printicus/For-Voron-Printers/MiniBurner_XL_Toolhead/Images/Pusher_example_location.jpg

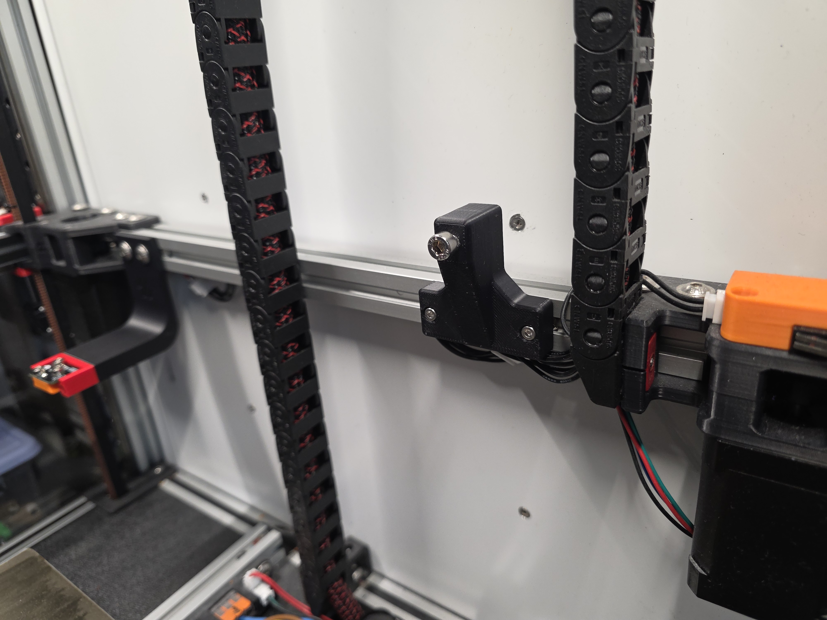
MiniBurner_XL_Toolhead/Images/Pusher_example_location.jpg
