printicus/For-Voron-Printers/MiniBurner_XL_Toolhead/Images/StealthChanger_Shuttle_04.jpg

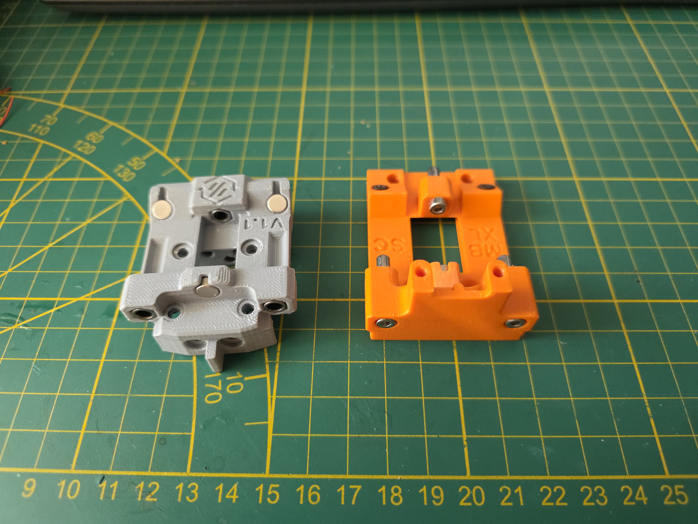
MiniBurner_XL_Toolhead/Images/StealthChanger_Shuttle_04.jpg
