printicus/For-Voron-Printers/MiniBurner_XL_Toolhead/Images/Toolhead_03.jpg

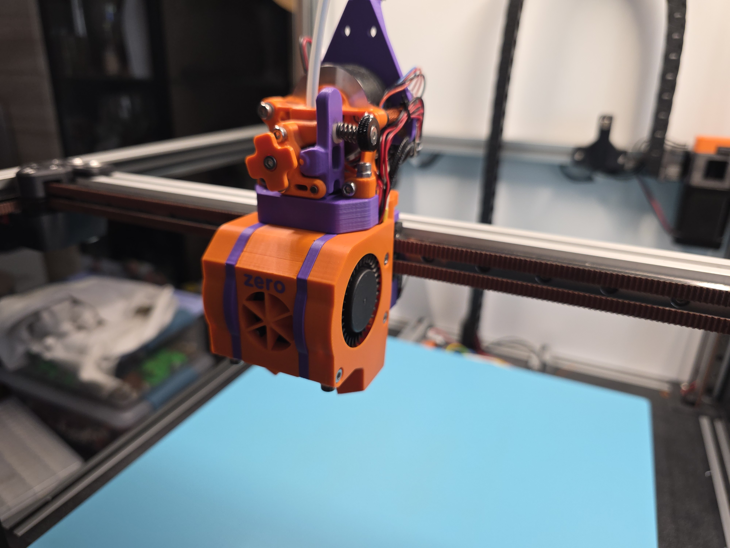
MiniBurner_XL_Toolhead/Images/Toolhead_03.jpg
