printicus/For-Voron-Printers/MiniBurner_XL_Toolhead/Images/Toolhead_05.jpg

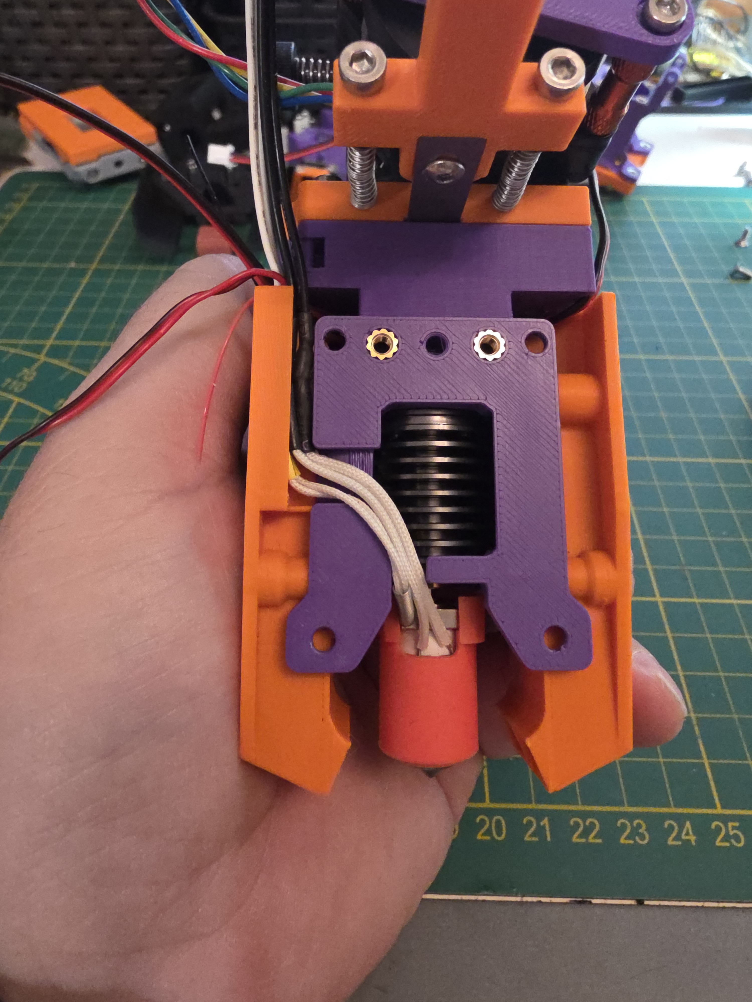
MiniBurner_XL_Toolhead/Images/Toolhead_05.jpg
