printicus/For-Voron-Printers/MiniBurner_XL_Toolhead/Images/Toolhead_06.jpg

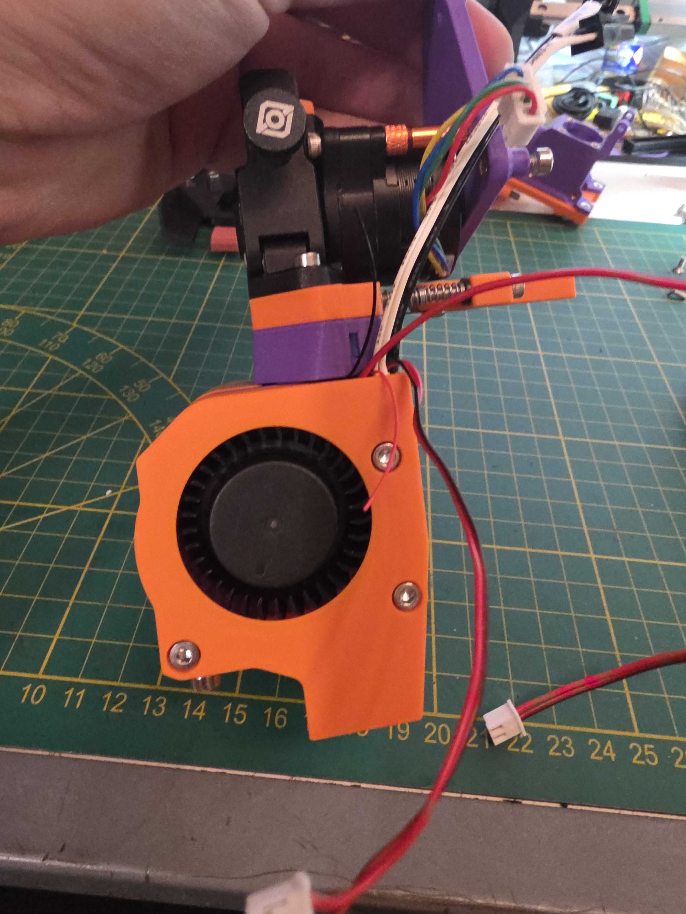
MiniBurner_XL_Toolhead/Images/Toolhead_06.jpg
