printicus/For-Voron-Printers/MiniBurner_XL_Toolhead/Images/Toolhead_08.jpg

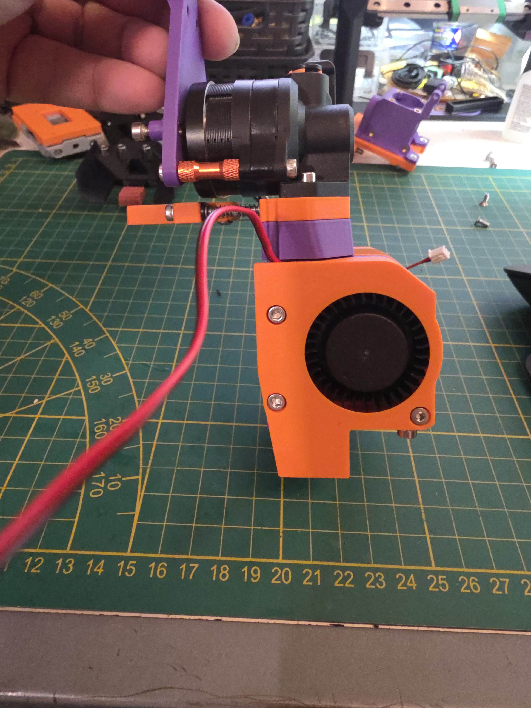
MiniBurner_XL_Toolhead/Images/Toolhead_08.jpg
