printicus/For-Voron-Printers/MiniBurner_XL_Toolhead/Images/Toolhead_09.jpg

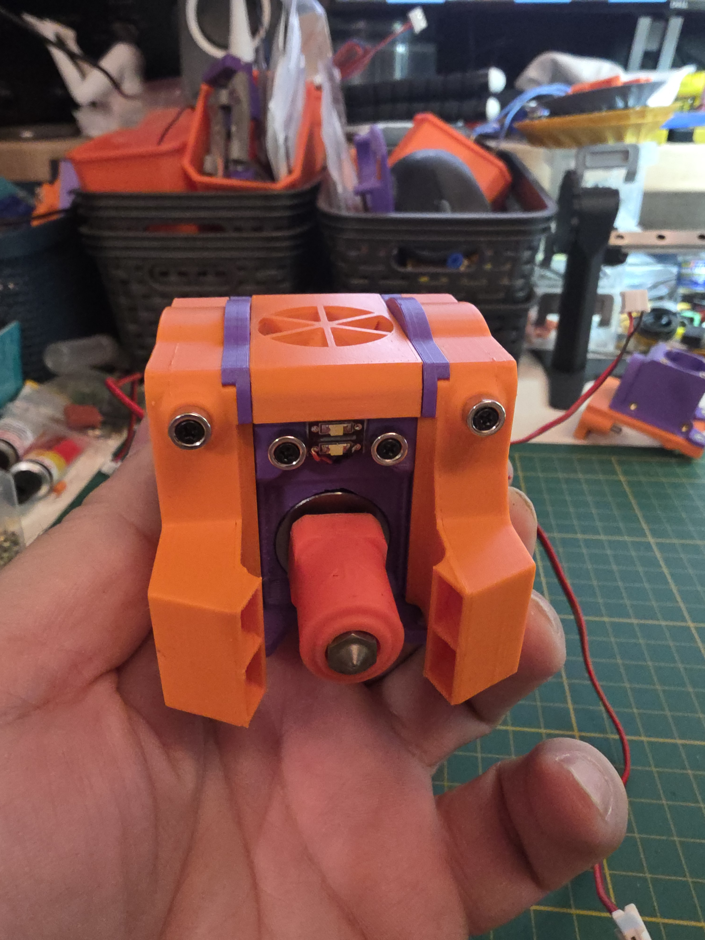
MiniBurner_XL_Toolhead/Images/Toolhead_09.jpg
