printicus/For-Voron-Printers/MiniBurner_XL_Toolhead/Images/Umbilical_01.jpg

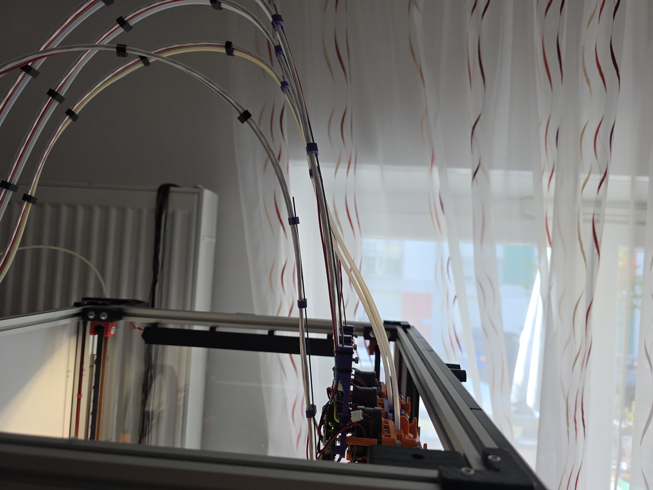
MiniBurner_XL_Toolhead/Images/Umbilical_01.jpg
