printicus/For-Voron-Printers/Voron 2.4 Left Front Skirt With Power Switch/Images/Image02.jpg

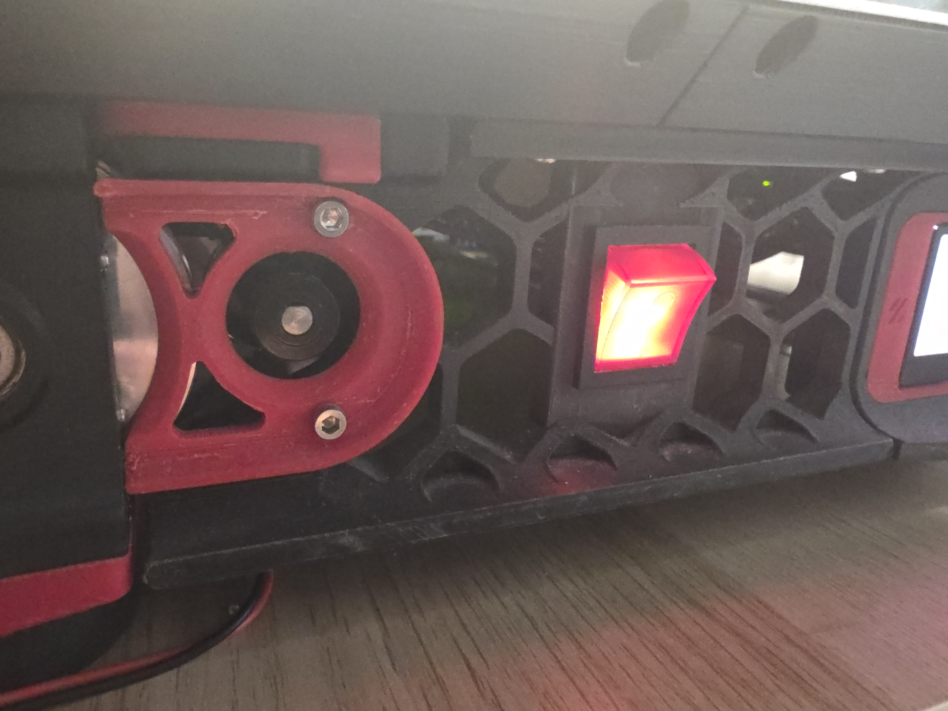
Voron 2.4 Left Front Skirt With Power Switch/Images/Image02.jpg
