printicus/For-Voron-Printers/Belt-Clamp-for-Voron-2.4-and-Trident/CAD/Left Side.step

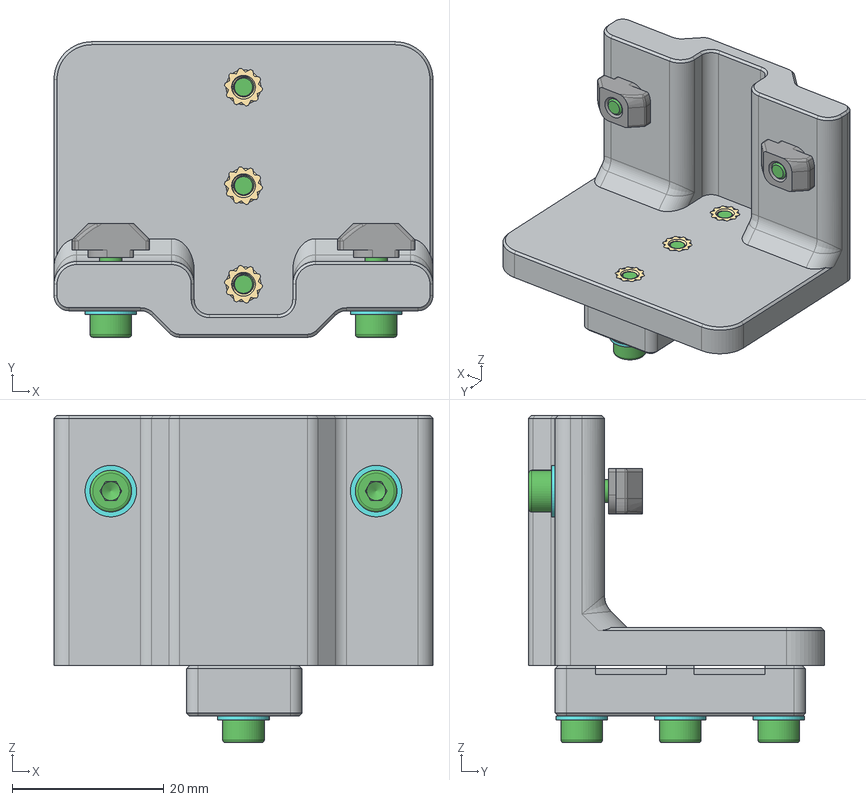
[picture p46: CAD file, 2025-07-18]
Belt-Clamp-for-Voron-2.4-and-Trident/CAD/Left Side.step
50.0 x 39.0 x 43.2 mm
XY belt clamp - left
Heat Insert M3 Short 5x4 x 3
XY belt clamp - common
M3 Washer x 5
M3x12 hex socket cap screw x 5
M3 Hammerhead T-Nut x 2
