printicus/For-Voron-Printers/Belt-Clamp-for-Voron-2.4-and-Trident/STL/XY belt clamp - right - part a.stl

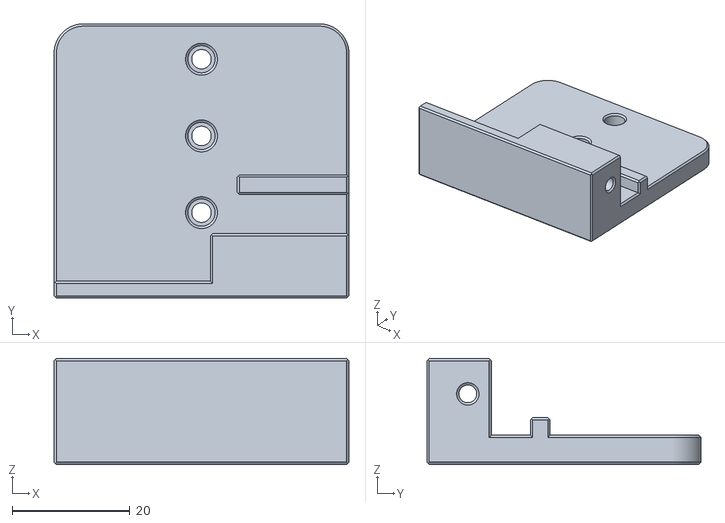
[picture p47: CAD file, 2025-07-19]
Belt-Clamp-for-Voron-2.4-and-Trident/STL/XY belt clamp - right - part a.stl
50.0 x 46.5 x 18.0
