printicus/For-Voron-Printers/MiniBurner_XL_Toolhead/STL/Extruders/For_Orbiter_v2/Orbiter_v2_CAN_PCB_Umbilical_Mount_for_max_2mm_wire.stl

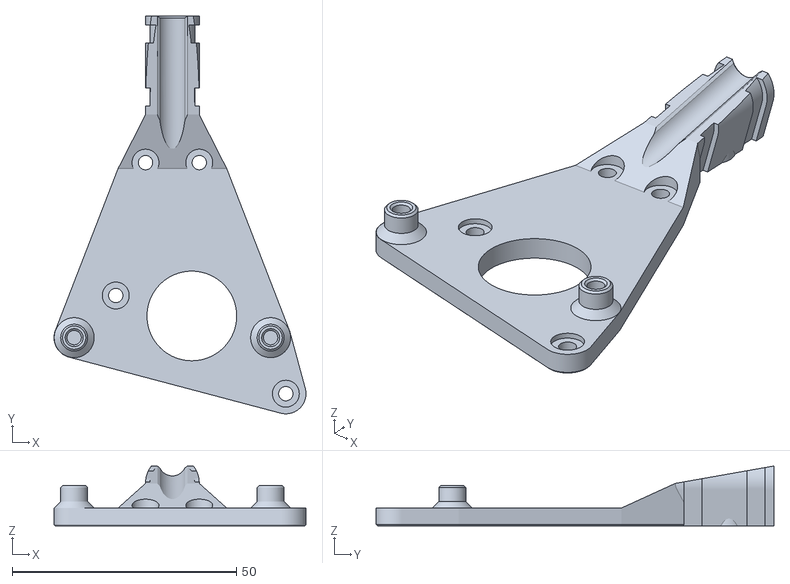
[picture p48: CAD file, 2025-08-24]
MiniBurner_XL_Toolhead/STL/Extruders/For_Orbiter_v2/Orbiter_v2_CAN_PCB_Umbilical_Mount_for_max_2mm_wire.stl
56.2 x 88.7 x 13.4
