printicus/For-Voron-Printers/MiniBurner_XL_Toolhead/STL/Extruders/For_Sherpa-Mini/Sherpa_Mini_CAN_PCB_Umbilical_Mount_for_max_2mm_wire.stl

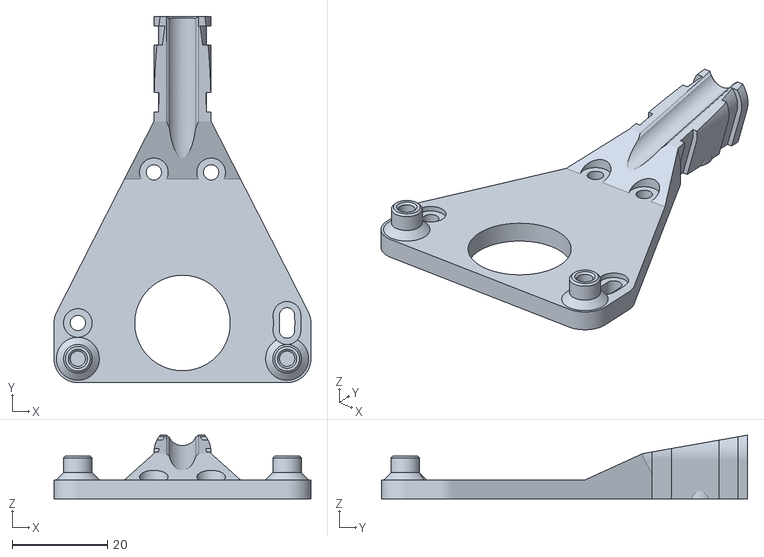
[picture p49: CAD file, 2025-08-24]
MiniBurner_XL_Toolhead/STL/Extruders/For_Sherpa-Mini/Sherpa_Mini_CAN_PCB_Umbilical_Mount_for_max_2mm_wire.stl
53.8 x 76.7 x 13.4
