printicus/For-Voron-Printers/MiniBurner_XL_Toolhead/STL/For_Volcano_Lenght_Nozzle/Right_Fan_Support_-_Sunon.stl

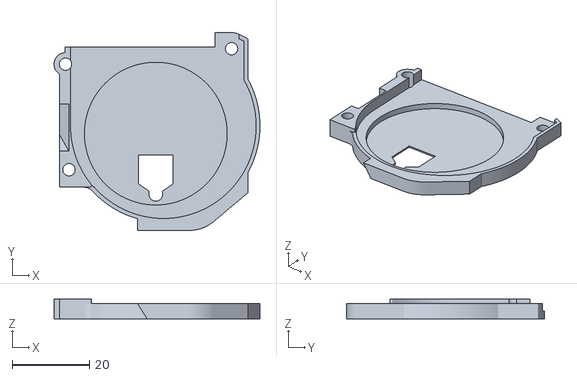
[picture p50: CAD file, 2025-08-24]
MiniBurner_XL_Toolhead/STL/For_Volcano_Lenght_Nozzle/Right_Fan_Support_-_Sunon.stl
53.4 x 51.3 x 5.10
