printicus/For-Voron-Printers/OV9726 Nozzle Camera/STL/Bottom.stl

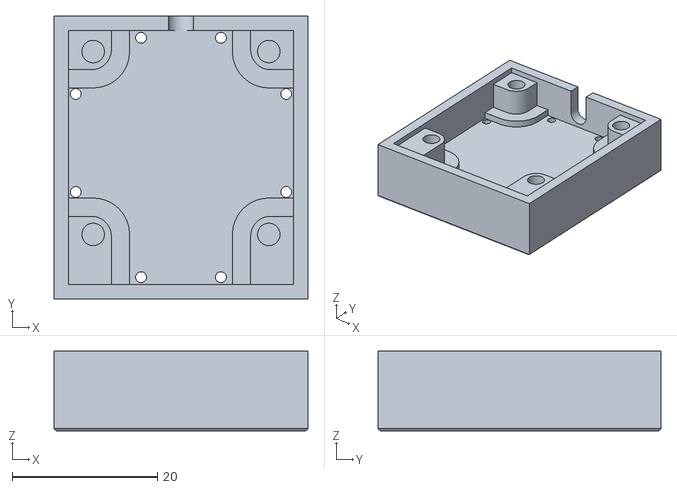
[picture p51: CAD file, 2025-07-21]
OV9726 Nozzle Camera/STL/Bottom.stl
35.0 x 39.0 x 11.0
