printicus/For-Voron-Printers/Voron 2.4 Left Front Skirt With Power Switch/CAD/front_skirt_a_300_with_power_switch-Body.step

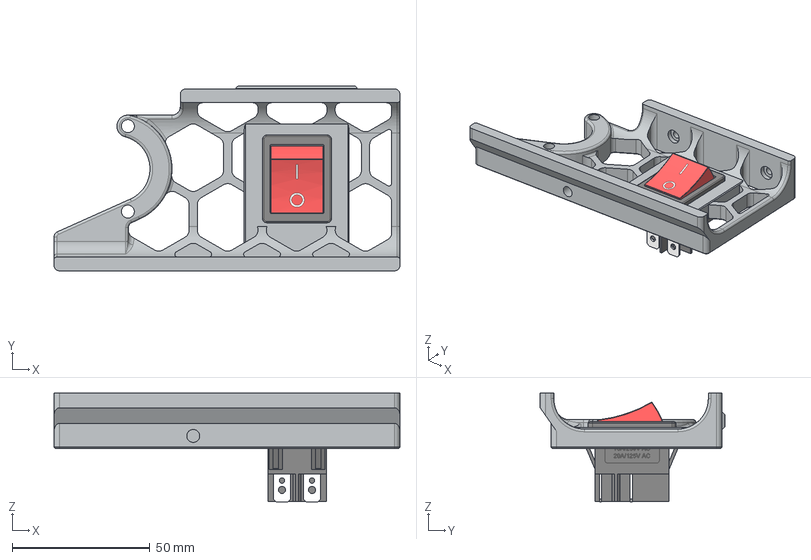
[picture p52: CAD file, 2025-07-19]
Voron 2.4 Left Front Skirt With Power Switch/CAD/front_skirt_a_300_with_power_switch-Body.step
125.5 x 67.0 x 39.4 mm
front_skirt_a_300_with_power_switch-Body
Case
Button
