printicus/For-Voron-Printers/Belt-Clamp-for-Voron-2.4-and-Trident/STL/XY belt clamp - left.stl

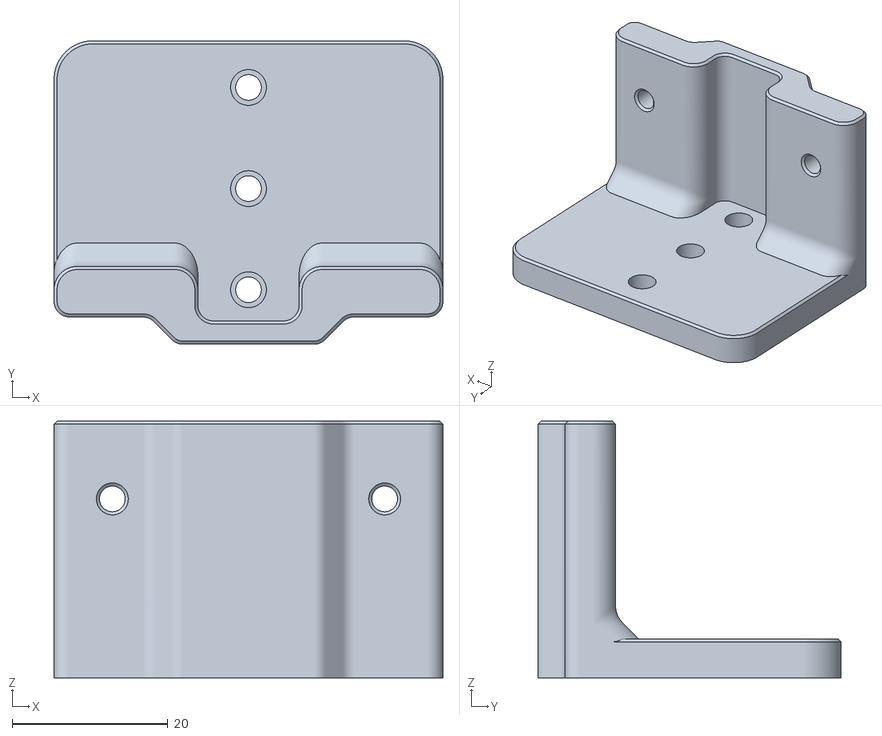
[picture p53: CAD file, 2025-07-18]
Belt-Clamp-for-Voron-2.4-and-Trident/STL/XY belt clamp - left.stl
50.0 x 39.0 x 33.0
