printicus/For-Voron-Printers/MiniBurner_XL_Toolhead/CAD/Extruders/Sherpa_Mini_CAN_PCB_Umbilical_Mount_for_3x0.3_flat_spring-steel.step

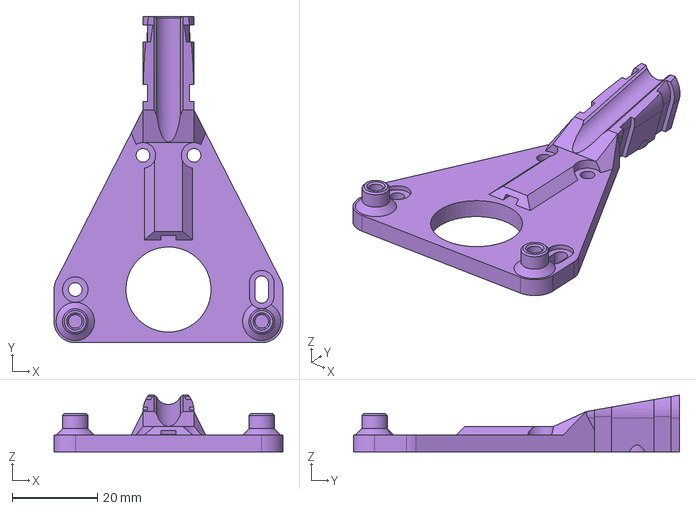
[picture p54: CAD file, 2025-08-24]
MiniBurner_XL_Toolhead/CAD/Extruders/Sherpa_Mini_CAN_PCB_Umbilical_Mount_for_3x0.3_flat_spring-steel.step
53.8 x 76.7 x 13.4 mm
