printicus/For-Voron-Printers/MiniBurner_XL_Toolhead/STL/Extruders/For_Orbiter_v2/Orbiter_v2_Support.stl

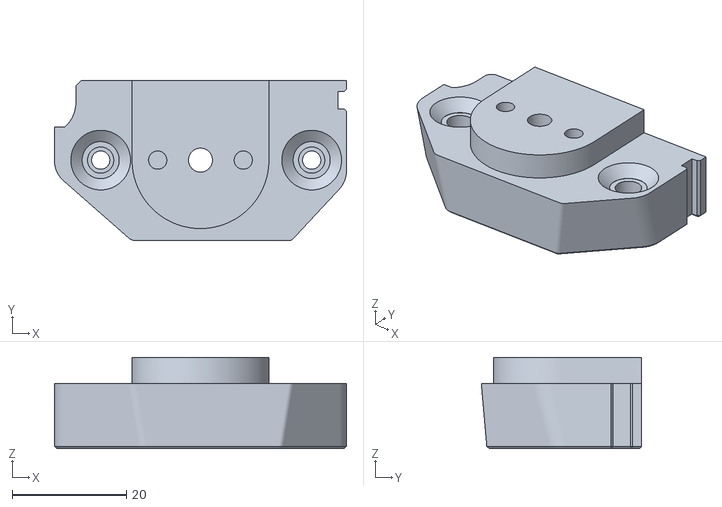
[picture p55: CAD file, 2025-08-24]
MiniBurner_XL_Toolhead/STL/Extruders/For_Orbiter_v2/Orbiter_v2_Support.stl
51.2 x 28.1 x 16.0
