printicus/For-Voron-Printers/Voron 2.4 Left Front Skirt With Power Switch/CAD/front_skirt_a_250_with_power_switch-Body.step

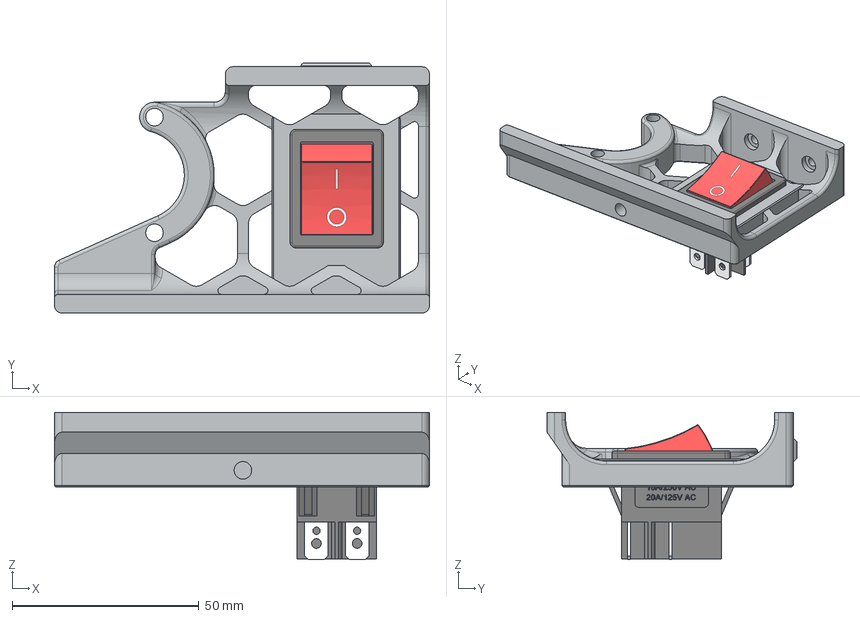
[picture p56: CAD file, 2025-07-19]
Voron 2.4 Left Front Skirt With Power Switch/CAD/front_skirt_a_250_with_power_switch-Body.step
100.5 x 67.0 x 39.4 mm
front_skirt_a_250_with_power_switch-Body
Case
Button
