printicus/For-Voron-Printers/Belt-Clamp-for-Voron-2.4-and-Trident/STL/XY belt clamp - common - x2.stl

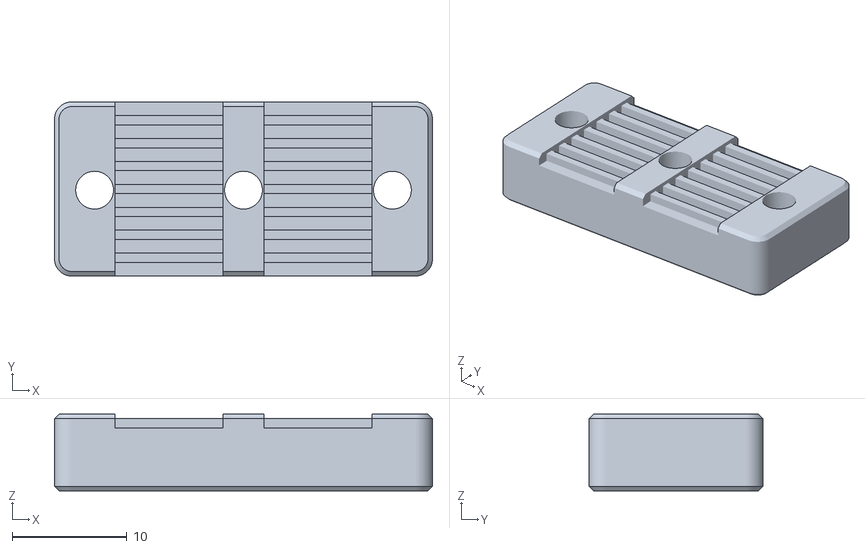
[picture p57: CAD file, 2025-07-18]
Belt-Clamp-for-Voron-2.4-and-Trident/STL/XY belt clamp - common - x2.stl
33.0 x 15.2 x 6.70
