printicus/For-Voron-Printers/MiniBurner_XL_Toolhead/STL/Extruders/For_Orbiter_v2/Orbiter_v2_Filament_Cutting_Adapter.stl

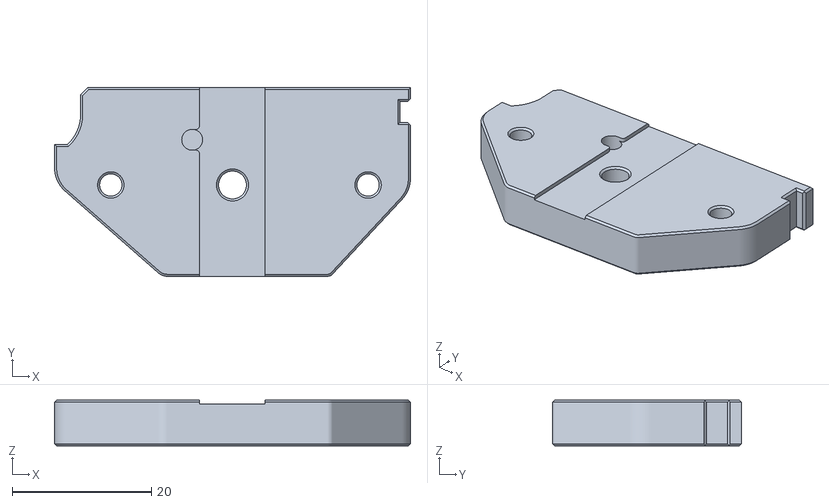
[picture p58: CAD file, 2025-08-24]
MiniBurner_XL_Toolhead/STL/Extruders/For_Orbiter_v2/Orbiter_v2_Filament_Cutting_Adapter.stl
51.2 x 27.1 x 6.60
