printicus/For-Voron-Printers/MiniBurner_XL_Toolhead/STL/Extruders/For_Sherpa-Mini/Sherpa_Mini_Filament_Cutting_Adapter.stl

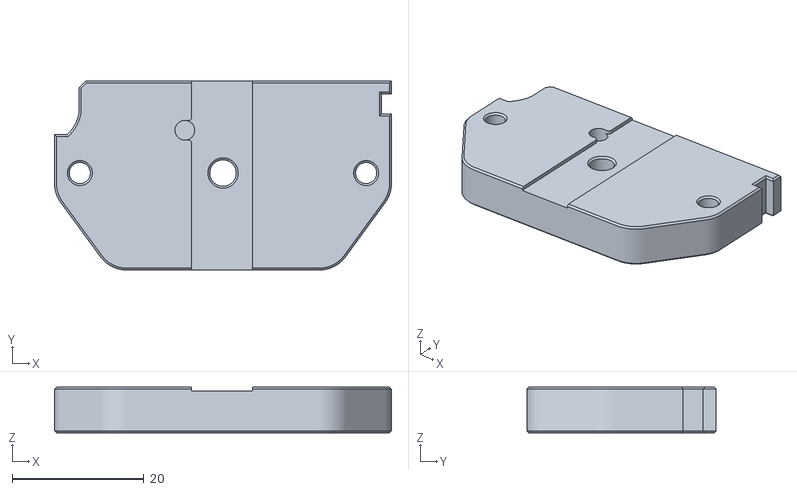
[picture p59: CAD file, 2025-08-24]
MiniBurner_XL_Toolhead/STL/Extruders/For_Sherpa-Mini/Sherpa_Mini_Filament_Cutting_Adapter.stl
51.2 x 28.7 x 6.95
