printicus/For-Voron-Printers/MiniBurner_XL_Toolhead/STL/For_Volcano_Lenght_Nozzle/Right_Fan_Cover_-_GDSTIME.stl

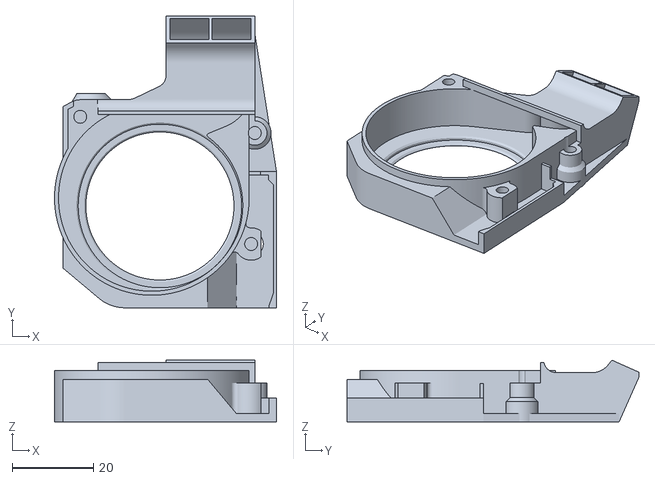
[picture p60: CAD file, 2025-08-24]
MiniBurner_XL_Toolhead/STL/For_Volcano_Lenght_Nozzle/Right_Fan_Cover_-_GDSTIME.stl
54.7 x 71.9 x 15.2
