printicus/For-Voron-Printers/MiniBurner_XL_Toolhead/STL/For_Volcano_Lenght_Nozzle/Front_Cover.stl

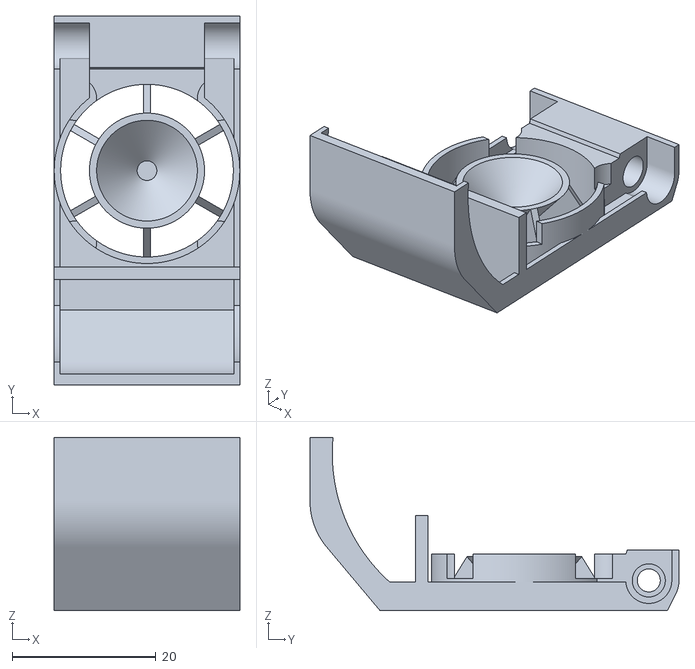
[picture p61: CAD file, 2025-08-24]
MiniBurner_XL_Toolhead/STL/For_Volcano_Lenght_Nozzle/Front_Cover.stl
25.8 x 51.3 x 24.1
